ruedli/DoctorWhoDalek/DalekHardware/Dalek3DPrint/Dalek mount2.jpg

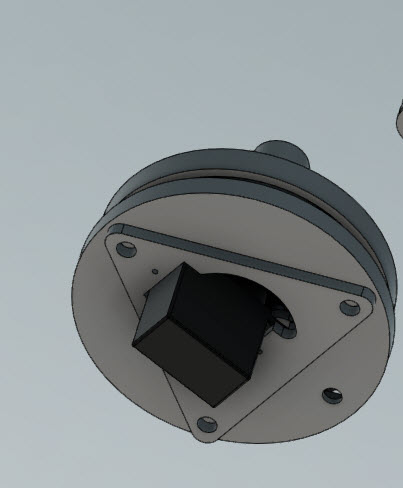
DalekHardware/Dalek3DPrint/Dalek mount2.jpg
