ruedli/DoctorWhoDalek/DalekHardware/Dalek3DPrint/TopperFitting.stl

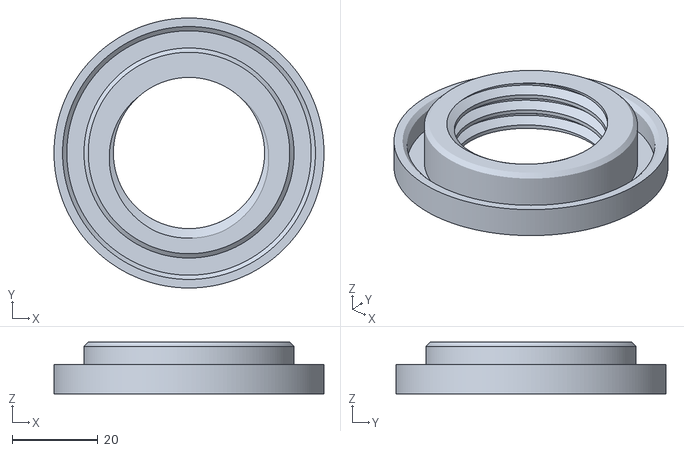
[picture p20: CAD file, 2022-04-21]
DalekHardware/Dalek3DPrint/TopperFitting.stl
63.0 x 63.0 x 12.1
