ruedli/DoctorWhoDalek/DalekHardware/Dalek3DPrint/Nut2.stl

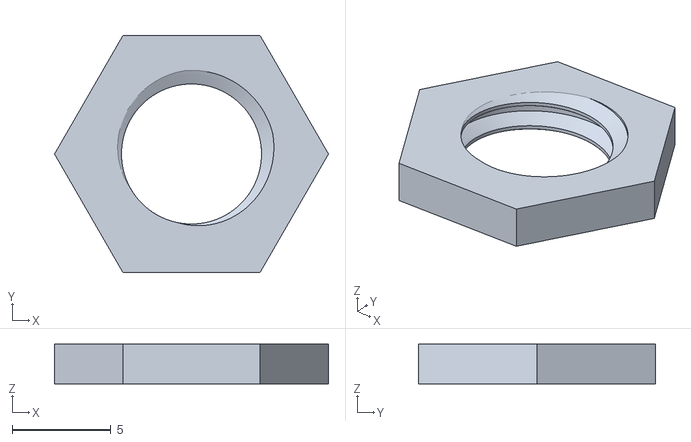
[picture p21: CAD file, 2022-04-21]
DalekHardware/Dalek3DPrint/Nut2.stl
13.9 x 12.0 x 2.01
