ruedli/DoctorWhoDalek/DalekHardware/Dalek3DPrint/Nut3.stl

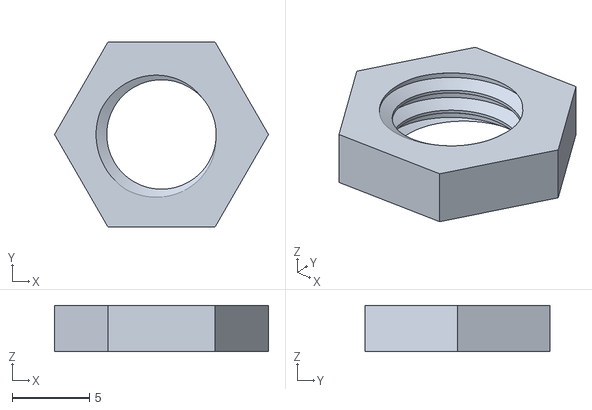
[picture p22: CAD file, 2022-04-21]
DalekHardware/Dalek3DPrint/Nut3.stl
13.9 x 12.0 x 3.00
