ruedli/DoctorWhoDalek/DalekHardware/Dalek3DPrint/LockingNut.stl

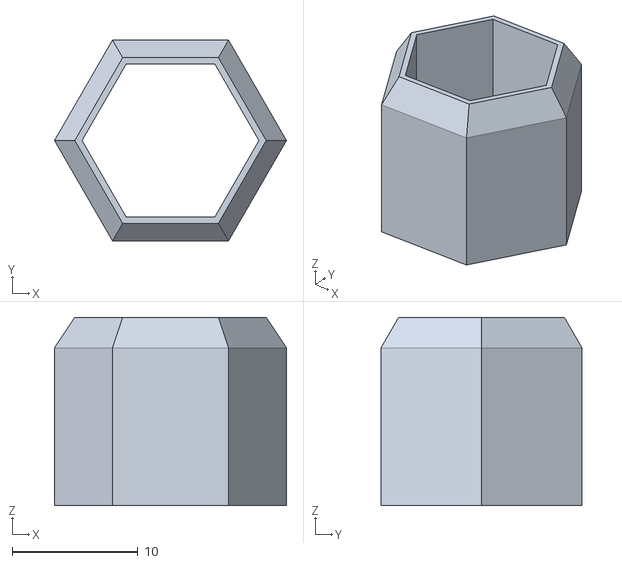
[picture p23: CAD file, 2022-04-21]
DalekHardware/Dalek3DPrint/LockingNut.stl
18.5 x 16.0 x 15.0
